Glutte/glutt-o-matique/doc/20151118-machine-etats.png

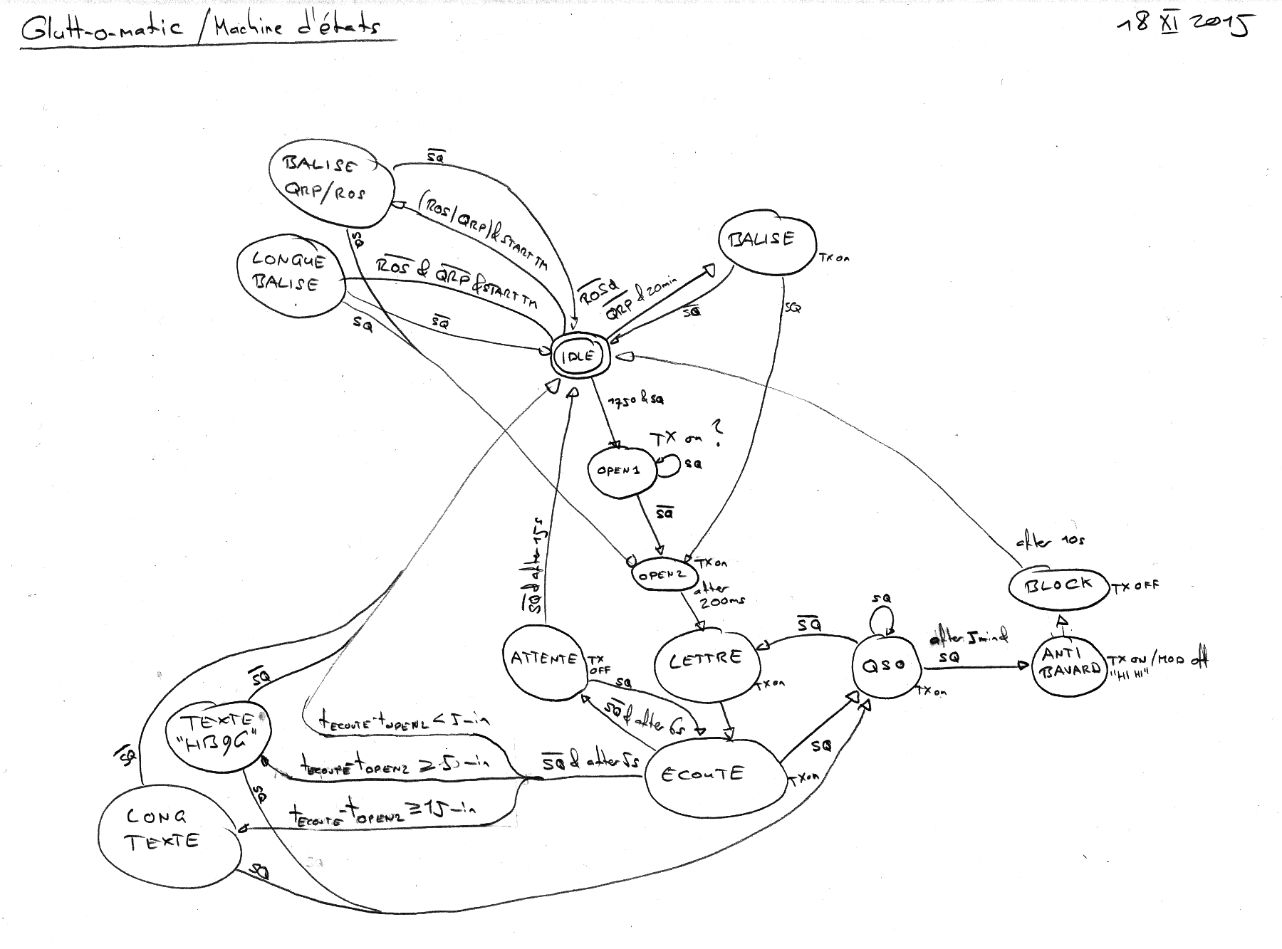
doc/20151118-machine-etats.png
