Glutte/glutt-o-matique/src/common/GPIO/leds.h

#pragma once

#define LED_GREEN 1
#define LED_ORANGE 2
#define LED_RED 3
#define LED_BLUE 4

void leds_turn_off(int);
void leds_turn_on(int);
