Glutte/glutt-o-matique/src/simulator/src/Gui/gui.c

/*
 * The MIT License (MIT)
 *
 * Copyright (c) 2016 Matthias P. Braendli, Maximilien Cuony
 *
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
 * THE SOFTWARE IS PROVIDED "AS IS", WITHOUT WARRANTY OF ANY KIND, EXPRESS OR
 * IMPLIED, INCLUDING BUT NOT LIMITED TO THE WARRANTIES OF MERCHANTABILITY,
 * FITNESS FOR A PARTICULAR PURPOSE AND NONINFRINGEMENT. IN NO EVENT SHALL THE
 * AUTHORS OR COPYRIGHT HOLDERS BE LIABLE FOR ANY CLAIM, DAMAGES OR OTHER
 * LIABILITY, WHETHER IN AN ACTION OF CONTRACT, TORT OR OTHERWISE, ARISING FROM,
 * OUT OF OR IN CONNECTION WITH THE SOFTWARE OR THE USE OR OTHER DEALINGS IN THE
 * SOFTWARE.
*/

#include "FreeRTOS.h"
#include "FreeRTOSConfig.h"
#include "task.h"

#include <stdio.h>
#include <stdlib.h>
#include <stdint.h>
#include <stdarg.h>
#include <string.h>
#include <math.h>
#include <assert.h>
#include <math.h>
#include <time.h>
#include <limits.h>

#include "gui.h"
#include "Core/common.h"

#define NK_INCLUDE_FIXED_TYPES
#define NK_INCLUDE_STANDARD_IO
#define NK_INCLUDE_DEFAULT_ALLOCATOR
#define NK_INCLUDE_VERTEX_BUFFER_OUTPUT
#define NK_INCLUDE_FONT_BAKING
#define NK_INCLUDE_DEFAULT_FONT
#define NK_IMPLEMENTATION
#define NK_XLIB_GL3_IMPLEMENTATION
#define NK_XLIB_LOAD_OPENGL_EXTENSIONS

#pragma GCC diagnostic push 
#pragma GCC diagnostic ignored "-Wunused-but-set-variable"
#pragma GCC diagnostic ignored "-Wunused-value"
#pragma GCC diagnostic ignored "-Wunused-function"
#include "nuklear.h"
#pragma GCC diagnostic pop

#include "nuklear_xlib_gl3.h"

#define WINDOW_WIDTH 1300
#define WINDOW_HEIGHT 800

#define MAX_VERTEX_BUFFER 512 * 1024
#define MAX_ELEMENT_BUFFER 128 * 1024

#define UNUSED(a) (void)a
#define MIN(a,b) ((a) < (b) ? (a) : (b))
#define MAX(a,b) ((a) < (b) ? (b) : (a))
#define LEN(a) (sizeof(a)/sizeof(a)[0])


/**
 * USART
 **/
char uart_recv_txt[4096];
static char uart_send_txt[512];
static int uart_send_txt_len;
void gui_usart_send(char*);

/**
 * Leds
 **/
char led_blue = 0;
char led_green = 0;
char led_orange = 0;
char led_red = 0;
char led_gps = 0;
char led_fax = 0;
char led_det_1750 = 0;
char led_sq2 = 0;

/**
 * GPS
 */
int gui_gps_send_frame = 0;
int gui_gps_frames_valid = 1;
char gui_gps_lat[64] = "4719.59788";
int gui_gps_lat_len = 10;
static const char *gps_NS[] = {"North", "South"};
int gui_gps_lat_hem = 0;
char gui_gps_lon[64] = "00830.92084";
int gui_gps_lon_len = 10;
static const char *gps_EW[] = {"East", "West"};
int gui_gps_lon_hem = 0;
int gui_gps_send_current_time = 1;
int gui_gps_custom_hour_on = 0;
int gui_gps_custom_min_on = 0;
int gui_gps_custom_sec_on = 0;
int gui_gps_custom_day_on = 0;
int gui_gps_custom_month_on = 0;
int gui_gps_custom_year_on = 0;
char gui_gps_custom_hour[4] = "12";
int gui_gps_custom_hour_len = 2;
char gui_gps_custom_min[4] = "30";
int gui_gps_custom_min_len = 2;
char gui_gps_custom_sec[4] = "45";
int gui_gps_custom_sec_len = 2;
char gui_gps_custom_day[4] = "01";
int gui_gps_custom_day_len = 2;
char gui_gps_custom_month[4] = "06";
int gui_gps_custom_month_len = 2;
char gui_gps_custom_year[4] = "16";
int gui_gps_custom_year_len = 2;


/**
 * Audio
 **/
char gui_cw_text[4096];


/**
 * Temperature
 **/
int gui_temperature_valid = 1;
float gui_temperature = 25.0;


/**
 * Outputs
 */
char gui_out_tx = 0;
char gui_out_mod_off = 0;
char gui_out_qrp = 0;


/**
 * Inputs
 */
int gui_in_button = 0;
int gui_in_qrp_n = 1;
int gui_in_1750_n = 1;
int gui_in_sq_n = 1;
int gui_in_u = 0;
int gui_in_d = 0;
int gui_in_replie = 0;
int gui_in_tone_1750 = 0;
static const char *replie_status[] = {"In vent", "Replié"};
int gui_in_fax_n = 1;

int in_button = 0;
int in_qrp_n = 1;
int in_1750_n = 1;
int in_sq_n = 1;
int in_u = 0;
int in_d = 0;
int in_fax_n = 1;


/**
 * FSM
 **/
const char * gui_last_fsm_states[] = {"", "", "", "", "", "", "", "", "", ""};
int gui_last_fsm_states_timestamps[] = {0, 0, 0, 0, 0, 0, 0, 0, 0, 0};


/**
 * Voltage and battery cap
 **/
float gui_measured_voltage = 14.0f;
int gui_measured_capacity = 1630; // Ah
int gui_measured_capacity_last = 1630; // Ah

static const char *breaker_status[] = {"Closed", "Open"};
static const char *breaker_message[] = {"On", "Off"};
int gui_breaker_status = 0;
int gui_breaker_status_last = 0;


/**
 * SWR
 **/
int gui_swr_forward;
int gui_swr_reflected;


int auto_scroll_uart = 1;
int auto_scroll_cw = 1;


struct XWindow {
    Display *dpy;
    Window win;
    XVisualInfo *vis;
    Colormap cmap;
    XSetWindowAttributes swa;
    XWindowAttributes attr;
    GLXFBConfig fbc;
    int width, height;
};

static int gl_err = FALSE;
static int gl_error_handler(Display __attribute__ ((unused))*dpy, XErrorEvent __attribute__ ((unused))*ev) {
    gl_err = TRUE;
    return 0;
}

static void die(const char *fmt, ...) {
    va_list ap;
    va_start(ap, fmt);
    vfprintf(stderr, fmt, ap);
    va_end(ap);
    fputs("\n", stderr);
    exit(EXIT_FAILURE);
}

static int has_extension(const char *string, const char *ext) {

    const char *start, *where, *term;
    where = strchr(ext, ' ');

    if (where || *ext == '\0')
        return FALSE;

    for (start = string;;) {
        where = strstr((const char*)start, ext);
        if (!where) break;

        term = where + strlen(ext);
        if (where == start || *(where - 1) == ' ') {
            if (*term == ' ' || *term == '\0') {
                return TRUE;
            }
        }
        start = term;
    }
    return FALSE;
}


void main_gui() {
    /* Platform */
    int running = 1;
    struct XWindow win;
    GLXContext glContext;
    struct nk_context *ctx;
    struct nk_color background;

    memset(&win, 0, sizeof(win));
    win.dpy = XOpenDisplay(NULL);

    if (!win.dpy) {
        die("Failed to open X display\n");
    }

    {
        /* check glx version */
        int glx_major, glx_minor;
        if (!glXQueryVersion(win.dpy, &glx_major, &glx_minor))
            die("[X11]: Error: Failed to query OpenGL version\n");
        if ((glx_major == 1 && glx_minor < 3) || (glx_major < 1))
            die("[X11]: Error: Invalid GLX version!\n");
    }

    {
        /* find and pick matching framebuffer visual */
        int fb_count;
        static GLint attr[] = {
            GLX_X_RENDERABLE,   True,
            GLX_DRAWABLE_TYPE,  GLX_WINDOW_BIT,
            GLX_RENDER_TYPE,    GLX_RGBA_BIT,
            GLX_X_VISUAL_TYPE,  GLX_TRUE_COLOR,
            GLX_RED_SIZE,       8,
            GLX_GREEN_SIZE,     8,
            GLX_BLUE_SIZE,      8,
            GLX_ALPHA_SIZE,     8,
            GLX_DEPTH_SIZE,     24,
            GLX_STENCIL_SIZE,   8,
            GLX_DOUBLEBUFFER,   True,
            None
        };
        GLXFBConfig *fbc;
        fbc = glXChooseFBConfig(win.dpy, DefaultScreen(win.dpy), attr, &fb_count);

        if (!fbc) {
            die("[X11]: Error: failed to retrieve framebuffer configuration\n");
        }

        {
            /* pick framebuffer with most samples per pixel */
            int i;
            int fb_best = -1;
            int best_num_samples = -1;

            for (i = 0; i < fb_count; ++i) {
                XVisualInfo *vi = glXGetVisualFromFBConfig(win.dpy, fbc[i]);
                if (vi) {
                    int sample_buffer, samples;
                    glXGetFBConfigAttrib(win.dpy, fbc[i], GLX_SAMPLE_BUFFERS, &sample_buffer);
                    glXGetFBConfigAttrib(win.dpy, fbc[i], GLX_SAMPLES, &samples);
                    if ((fb_best < 0) || (sample_buffer && samples > best_num_samples)) {
                        fb_best = i; best_num_samples = samples;
                    }
                }
            }
            win.fbc = fbc[fb_best];
            XFree(fbc);
            win.vis = glXGetVisualFromFBConfig(win.dpy, win.fbc);
        }
    }
    {
        /* create window */
        win.cmap = XCreateColormap(win.dpy, RootWindow(win.dpy, win.vis->screen), win.vis->visual, AllocNone);
        win.swa.colormap =  win.cmap;
        win.swa.background_pixmap = None;
        win.swa.border_pixel = 0;
        win.swa.event_mask =
            ExposureMask | KeyPressMask | KeyReleaseMask |
            ButtonPress | ButtonReleaseMask| ButtonMotionMask |
            Button1MotionMask | Button3MotionMask | Button4MotionMask | Button5MotionMask|
            PointerMotionMask| StructureNotifyMask;

        win.win = XCreateWindow(win.dpy, RootWindow(win.dpy, win.vis->screen), 0, 0,
                WINDOW_WIDTH, WINDOW_HEIGHT, 0, win.vis->depth, InputOutput,
                win.vis->visual, CWBorderPixel|CWColormap|CWEventMask, &win.swa);

        if (!win.win) die("[X11]: Failed to create window\n");
        XFree(win.vis);
        XStoreName(win.dpy, win.win, "glutt-o-matique simulator 3000");
        XMapWindow(win.dpy, win.win);
    }
    {
        /* create opengl context */
        typedef GLXContext(*glxCreateContext)(Display*, GLXFBConfig, GLXContext, Bool, const int*);
        int(*old_handler)(Display*, XErrorEvent*) = XSetErrorHandler(gl_error_handler);
        const char *extensions_str = glXQueryExtensionsString(win.dpy, DefaultScreen(win.dpy));
        glxCreateContext create_context = (glxCreateContext)
            glXGetProcAddressARB((const GLubyte*)"glXCreateContextAttribsARB");

        gl_err = FALSE;
        if (!has_extension(extensions_str, "GLX_ARB_create_context") || !create_context) {
            fprintf(stdout, "[X11]: glXCreateContextAttribARB() not found...\n");
            fprintf(stdout, "[X11]: ... using old-style GLX context\n");
            glContext = glXCreateNewContext(win.dpy, win.fbc, GLX_RGBA_TYPE, 0, True);
        } else {
            GLint attr[] = {
                GLX_CONTEXT_MAJOR_VERSION_ARB, 3,
                GLX_CONTEXT_MINOR_VERSION_ARB, 0,
                None
            };
            glContext = create_context(win.dpy, win.fbc, 0, True, attr);
            XSync(win.dpy, False);
            if (gl_err || !glContext) {
                /* Could not create GL 3.0 context. Fallback to old 2.x context.
                 * If a version below 3.0 is requested, implementations will
                 * return the newest context version compatible with OpenGL
                 * version less than version 3.0.*/
                attr[1] = 1; attr[3] = 0;
                gl_err = FALSE;
                fprintf(stdout, "[X11] Failed to create OpenGL 3.0 context\n");
                fprintf(stdout, "[X11] ... using old-style GLX context!\n");
                glContext = create_context(win.dpy, win.fbc, 0, True, attr);
            }
        }
        XSync(win.dpy, False);
        XSetErrorHandler(old_handler);
        if (gl_err || !glContext)
            die("[X11]: Failed to create an OpenGL context\n");
        glXMakeCurrent(win.dpy, win.win, glContext);
    }

    ctx = nk_x11_init(win.dpy, win.win);
    /* Load Fonts: if none of these are loaded a default font will be used  */
    {struct nk_font_atlas *atlas;
        nk_x11_font_stash_begin(&atlas);
        nk_x11_font_stash_end();
    }


    background = nk_rgb(28,48,62);

    while (running)
    {
        taskYIELD();

        vTaskSuspendAll();

        /* Input */
        XEvent evt;
        nk_input_begin(ctx);
        while (XCheckWindowEvent(win.dpy, win.win, win.swa.event_mask, &evt)){
            if (XFilterEvent(&evt, win.win)) continue;
            nk_x11_handle_event(&evt);
        }
        nk_input_end(ctx);

        /* GUI */
        {

            struct nk_panel layout;
            int nb_lines = 0;

            if (nk_begin(ctx, &layout, "UART", nk_rect(50, 50, 450, 330), NK_WINDOW_BORDER|NK_WINDOW_MOVABLE|NK_WINDOW_SCALABLE|NK_WINDOW_MINIMIZABLE|NK_WINDOW_TITLE)) {


                nk_menubar_begin(ctx);
                nk_layout_row_begin(ctx, NK_STATIC, 25, 2);
                nk_layout_row_push(ctx, 280);

                int active = nk_edit_string(ctx, NK_EDIT_FIELD|NK_EDIT_SIG_ENTER, uart_send_txt, &uart_send_txt_len, 512,  nk_filter_default);

                nk_layout_row_push(ctx, 70);
                if (nk_button_label(ctx, "Send", NK_BUTTON_DEFAULT) || (active & NK_EDIT_COMMITED)) {

                    uart_send_txt[uart_send_txt_len] = '\0';

                    gui_usart_send(uart_send_txt);

                    uart_send_txt[0] = '\0';
                    uart_send_txt_len = 0;
                }


                nk_layout_row_dynamic(ctx, 25, 2);
                nk_label(ctx, "UART Output:", NK_TEXT_LEFT);
                nk_checkbox_label(ctx, "(Auto scroll)", &auto_scroll_uart);

                nk_menubar_end(ctx);

                nk_layout_row_dynamic(ctx, 16, 1);

                char * current_pointer = uart_recv_txt;
                int l = 0;

                while (*current_pointer != 0) {

                    if (*current_pointer == '\n') {
                        if (l > 1) {
                            nk_text(ctx, current_pointer - l, l, NK_TEXT_LEFT);
                            nb_lines++;
                        }
                        current_pointer++;
                        l = 0;
                    }
                    current_pointer++;
                    l++;
                }

                if (l > 1) {
                    nk_text(ctx, current_pointer - l, l, NK_TEXT_LEFT);
                    nb_lines++;
                }
            }
            if (auto_scroll_uart) {
                layout.offset->y = nb_lines * 32 + 200;
            }
            nk_end(ctx);


            if (nk_begin(ctx, &layout, "LEDs", nk_rect(50, 390, 150, 155), NK_WINDOW_BORDER|NK_WINDOW_MOVABLE|NK_WINDOW_SCALABLE|NK_WINDOW_MINIMIZABLE|NK_WINDOW_TITLE)) {

                nk_layout_row_static(ctx, 20, 20, 5);
                struct nk_color color;

                color.r = 255; color.g = 165; color.b = 0;
                if (led_orange == 1) {
                    color.a = 255;
                } else {
                    color.a = 30;
                }
                nk_button_color(ctx, color, NK_BUTTON_DEFAULT);

                color.r = 0; color.g = 255; color.b = 0;
                if (led_green == 1) {
                    color.a = 255;
                } else {
                    color.a = 30;
                }
                nk_button_color(ctx, color, NK_BUTTON_DEFAULT);

                color.r = 255; color.g = 0; color.b = 0;
                if (led_red == 1) {
                    color.a = 255;
                } else {
                    color.a = 30;
                }
                nk_button_color(ctx, color, NK_BUTTON_DEFAULT);

                color.r = 0; color.g = 0; color.b = 255;
                if (led_blue == 1) {
                    color.a = 255;
                } else {
                    color.a = 30;
                }
                nk_button_color(ctx, color, NK_BUTTON_DEFAULT);

#define SW_LED(var, name) \
                nk_layout_row_static(ctx, 20, 20, 5); \
                color.r = 0; color.g = 255; color.b = 255; \
                if (var == 1) { color.a = 255; } else { color.a = 30; } \
                nk_button_color(ctx, color, NK_BUTTON_DEFAULT); \
                nk_label(ctx, name, NK_TEXT_LEFT);

                SW_LED(led_gps, "GPS")
                SW_LED(led_fax, "FAX")
                SW_LED(led_det_1750, "TONE")
                SW_LED(led_sq2, "SQ2")

            }
            nk_end(ctx);

            if (nk_begin(ctx, &layout, "CW", nk_rect(320, 390, 180, 155), NK_WINDOW_BORDER|NK_WINDOW_MOVABLE|NK_WINDOW_SCALABLE|NK_WINDOW_MINIMIZABLE|NK_WINDOW_TITLE)) {

                nk_menubar_begin(ctx);
                nk_layout_row_dynamic(ctx, 25, 2);

                nk_label(ctx, "CW Buffer:", NK_TEXT_LEFT);
                nk_checkbox_label(ctx, "(Auto scroll)", &auto_scroll_cw);

                nk_menubar_end(ctx);

                nk_layout_row_dynamic(ctx, 16, 1);

                char * current_pointer = gui_cw_text;
                int l = 0;
                nb_lines = 0;

                while (*current_pointer != 0) {

                    if (*current_pointer == '\n') {
                        if (l > 1) {
                            nk_text(ctx, current_pointer - l, l, NK_TEXT_LEFT);
                            nb_lines++;
                        }
                        current_pointer++;
                        l = 0;
                    }
                    current_pointer++;
                    l++;
                }

                if (l > 1) {
                    nk_text(ctx, current_pointer - l, l, NK_TEXT_LEFT);
                    nb_lines++;
                }
            }
            if (auto_scroll_uart) {
                layout.offset->y = nb_lines * 32 + 200;
            }
            nk_end(ctx);

            if (nk_begin(ctx, &layout, "GPS", nk_rect(510, 50, 200, 500), NK_WINDOW_BORDER|NK_WINDOW_MOVABLE|NK_WINDOW_MINIMIZABLE|NK_WINDOW_TITLE)) {

                nk_layout_row_dynamic(ctx, 30, 1);
                nk_checkbox_label(ctx, "Send frames", &gui_gps_send_frame);
                nk_checkbox_label(ctx, "Valid frames", &gui_gps_frames_valid);

                nk_layout_row_dynamic(ctx, 30, 2);

                nk_label(ctx, "Latitude:", NK_TEXT_LEFT);
                nk_edit_string(ctx, NK_EDIT_SIMPLE, gui_gps_lat, &gui_gps_lat_len, 64, nk_filter_float);
                nk_label(ctx, "", NK_TEXT_LEFT);
                gui_gps_lat_hem = nk_combo(ctx, gps_NS, LEN(gps_NS), gui_gps_lat_hem, 30);

                nk_label(ctx, "Longitude:", NK_TEXT_LEFT);
                nk_edit_string(ctx, NK_EDIT_SIMPLE, gui_gps_lon, &gui_gps_lon_len, 64, nk_filter_float);
                nk_label(ctx, "", NK_TEXT_LEFT);
                gui_gps_lon_hem = nk_combo(ctx, gps_EW, LEN(gps_EW), gui_gps_lon_hem, 30);

                nk_layout_row_dynamic(ctx, 30, 1);
                nk_checkbox_label(ctx, "Send current time", &gui_gps_send_current_time);

                if (!gui_gps_send_current_time) {

                    nk_label(ctx, "Custom values:", NK_TEXT_LEFT);

                    nk_layout_row_dynamic(ctx, 30, 3);

                    nk_label(ctx, "Hour", NK_TEXT_LEFT);
                    nk_checkbox_label(ctx, "", &gui_gps_custom_hour_on);
                    if (gui_gps_custom_hour_on) {
                        nk_edit_string(ctx, NK_EDIT_SIMPLE, gui_gps_custom_hour, &gui_gps_custom_hour_len, 3, nk_filter_decimal);
                    } else {
                        nk_label(ctx, "", NK_TEXT_LEFT);
                    }
                    nk_label(ctx, "Minutes", NK_TEXT_LEFT);
                    nk_checkbox_label(ctx, "", &gui_gps_custom_min_on);
                    if (gui_gps_custom_min_on) {
                        nk_edit_string(ctx, NK_EDIT_SIMPLE, gui_gps_custom_min, &gui_gps_custom_min_len, 3, nk_filter_decimal);
                    } else {
                        nk_label(ctx, "", NK_TEXT_LEFT);
                    }
                    nk_label(ctx, "Secondes", NK_TEXT_LEFT);
                    nk_checkbox_label(ctx, "", &gui_gps_custom_sec_on);
                    if (gui_gps_custom_sec_on) {
                        nk_edit_string(ctx, NK_EDIT_SIMPLE, gui_gps_custom_sec, &gui_gps_custom_sec_len, 3, nk_filter_decimal);
                    } else {
                        nk_label(ctx, "", NK_TEXT_LEFT);
                    }
                    nk_label(ctx, "Day", NK_TEXT_LEFT);
                    nk_checkbox_label(ctx, "", &gui_gps_custom_day_on);
                    if (gui_gps_custom_day_on) {
                        nk_edit_string(ctx, NK_EDIT_SIMPLE, gui_gps_custom_day, &gui_gps_custom_day_len, 3, nk_filter_decimal);
                    } else {
                        nk_label(ctx, "", NK_TEXT_LEFT);
                    }
                    nk_label(ctx, "Month", NK_TEXT_LEFT);
                    nk_checkbox_label(ctx, "", &gui_gps_custom_month_on);
                    if (gui_gps_custom_month_on) {
                        nk_edit_string(ctx, NK_EDIT_SIMPLE, gui_gps_custom_month, &gui_gps_custom_month_len, 3, nk_filter_decimal);
                    } else {
                        nk_label(ctx, "", NK_TEXT_LEFT);
                    }
                    nk_label(ctx, "Year", NK_TEXT_LEFT);
                    nk_checkbox_label(ctx, "", &gui_gps_custom_year_on);
                    if (gui_gps_custom_year_on) {
                        nk_edit_string(ctx, NK_EDIT_SIMPLE, gui_gps_custom_year, &gui_gps_custom_year_len, 3, nk_filter_decimal);
                    } else {
                        nk_label(ctx, "", NK_TEXT_LEFT);
                    }


                }

            }
            nk_end(ctx);


            if (nk_begin(ctx, &layout, "Output", nk_rect(720, 510, 200, 170), NK_WINDOW_BORDER|NK_WINDOW_MOVABLE|NK_WINDOW_MINIMIZABLE|NK_WINDOW_TITLE)) {

                nk_layout_row_dynamic(ctx, 25, 2);

                struct nk_color color;

                nk_label(ctx, "TX", NK_TEXT_LEFT);

                color.r = 0; color.g = 255; color.b = 0;

                if (gui_out_tx == 1) {
                    color.a = 255;
                } else {
                    color.a = 30;
                }
                nk_button_color(ctx, color, NK_BUTTON_DEFAULT);

                nk_label(ctx, "Mod OFF", NK_TEXT_LEFT);

                color.r = 255; color.g = 255; color.b = 0;

                if (gui_out_mod_off == 1) {
                    color.a = 255;
                } else {
                    color.a = 30;
                }
                nk_button_color(ctx, color, NK_BUTTON_DEFAULT);

                nk_label(ctx, "QRP", NK_TEXT_LEFT);

                color.r = 255; color.g = 0; color.b = 0;

                if (gui_out_qrp == 1) {
                    color.a = 255;
                } else {
                    color.a = 30;
                }
                nk_button_color(ctx, color, NK_BUTTON_DEFAULT);

            }
            nk_end(ctx);

            if (nk_begin(ctx, &layout, "Input", nk_rect(720, 50, 200, 460), NK_WINDOW_BORDER|NK_WINDOW_MOVABLE|NK_WINDOW_MINIMIZABLE|NK_WINDOW_TITLE)) {

                nk_layout_row_dynamic(ctx, 25, 3);

                struct nk_color color_on = nk_rgb(0, 255, 0);
                struct nk_color color_off = nk_rgb(255, 0, 0);

                struct nk_color c;

                if (gui_in_button) {
                    c = color_on;
                } else {
                    c = color_off;
                }

                nk_label_colored(ctx, "Button", NK_TEXT_LEFT, c);
                nk_checkbox_label(ctx, "", &in_button);

                if (nk_button_label(ctx, "", NK_BUTTON_REPEATER)) {
                    gui_in_button = !in_button;
                } else {
                    gui_in_button = in_button;
                }

                if (gui_in_qrp_n) {
                    c = color_on;
                } else {
                    c = color_off;
                }

                nk_label_colored(ctx, "QRP_n", NK_TEXT_LEFT, c);
                nk_checkbox_label(ctx, "", &in_qrp_n);

                if (nk_button_label(ctx, "", NK_BUTTON_REPEATER)) {
                    gui_in_qrp_n = !in_qrp_n;
                } else {
                    gui_in_qrp_n = in_qrp_n;
                }

                if (gui_in_1750_n) {
                    c = color_on;
                } else {
                    c = color_off;
                }

                nk_label_colored(ctx, "1750 btn", NK_TEXT_LEFT, c);
                nk_checkbox_label(ctx, "", &in_1750_n);

                if (nk_button_label(ctx, "", NK_BUTTON_REPEATER)) {
                    gui_in_1750_n = !in_1750_n;
                } else {
                    gui_in_1750_n = in_1750_n;
                }

                if (gui_in_sq_n) {
                    c = color_on;
                } else {
                    c = color_off;
                }

                nk_label_colored(ctx, "SQ_n", NK_TEXT_LEFT, c);
                nk_checkbox_label(ctx, "", &in_sq_n);

                if (nk_button_label(ctx, "", NK_BUTTON_REPEATER)) {
                    gui_in_sq_n = !in_sq_n;
                } else {
                    gui_in_sq_n = in_sq_n;
                }

                if (gui_in_u) {
                    c = color_on;
                } else {
                    c = color_off;
                }

                nk_label_colored(ctx, "U", NK_TEXT_LEFT, c);
                nk_checkbox_label(ctx, "", &in_u);

                if (nk_button_label(ctx, "", NK_BUTTON_REPEATER)) {
                    gui_in_u = !in_u;
                } else {
                    gui_in_u = in_u;
                }

                if (gui_in_d) {
                    c = color_on;
                } else {
                    c = color_off;
                }

                nk_label_colored(ctx, "D", NK_TEXT_LEFT, c);
                nk_checkbox_label(ctx, "", &in_d);

                if (nk_button_label(ctx, "", NK_BUTTON_REPEATER)) {
                    gui_in_d = !in_d;
                } else {
                    gui_in_d = in_d;
                }

                if (gui_in_fax_n) {
                    c = color_on;
                } else {
                    c = color_off;
                }

                nk_label_colored(ctx, "FAX_n", NK_TEXT_LEFT, c);
                nk_checkbox_label(ctx, "", &in_fax_n);

                if (nk_button_label(ctx, "", NK_BUTTON_REPEATER)) {
                    gui_in_fax_n = !in_fax_n;
                } else {
                    gui_in_fax_n = in_fax_n;
                }

                if (gui_in_replie) {
                    c = color_on;
                } else {
                    c = color_off;
                }

                nk_layout_row_dynamic(ctx, 18, 2);
                nk_label_colored(ctx, "REPLIE", NK_TEXT_LEFT, c);
                gui_in_replie = nk_combo(ctx, replie_status, LEN(replie_status), gui_in_replie, 30);

                nk_label_colored(ctx, "Voltage", NK_TEXT_LEFT, c);
                nk_property_float(ctx, "V", 0.0f, &gui_measured_voltage, 24.0f, 0.5f, 0.5f);

                nk_layout_row_dynamic(ctx, 25, 2);
                nk_label_colored(ctx, "Eolienne breaker", NK_TEXT_LEFT, c);
                gui_breaker_status = nk_combo(ctx, breaker_status, LEN(breaker_status), gui_breaker_status, 30);

                if (gui_breaker_status != gui_breaker_status_last) {
                    uart_send_txt_len = snprintf(uart_send_txt, sizeof(uart_send_txt), "DISJEOL,%ld,%s", timestamp_now()/1000, breaker_message[gui_breaker_status]);

                    uart_send_txt[uart_send_txt_len] = '\0';
                    gui_usart_send(uart_send_txt);

                    gui_breaker_status_last = gui_breaker_status;
                }

                nk_layout_row_dynamic(ctx, 25, 2);
                nk_label_colored(ctx, "Capacity", NK_TEXT_LEFT, c);
                nk_property_int(ctx, "Ah", 0, &gui_measured_capacity, 1650, 10, 0.1f);

                if (gui_measured_capacity != gui_measured_capacity_last) {
                    uart_send_txt_len = snprintf(uart_send_txt, sizeof(uart_send_txt), "CAPA,%ld,%d", timestamp_now()/1000, gui_measured_capacity * 1000);

                    uart_send_txt[uart_send_txt_len] = '\0';
                    gui_usart_send(uart_send_txt);

                    gui_measured_capacity_last = gui_measured_capacity;
                }

                if (gui_in_tone_1750) {
                    c = color_on;
                } else {
                    c = color_off;
                }

                nk_label_colored(ctx, "TONE_1750", NK_TEXT_LEFT, c);


            }
            nk_end(ctx);

            if (nk_begin(ctx, &layout, "Temperature", nk_rect(930, 50, 200, 140), NK_WINDOW_BORDER|NK_WINDOW_MOVABLE|NK_WINDOW_MINIMIZABLE|NK_WINDOW_TITLE)) {

                nk_layout_row_dynamic(ctx, 25, 1);

                nk_checkbox_label(ctx, "Valid temperature", &gui_temperature_valid);

                if (gui_temperature_valid) {

                    nk_layout_row_dynamic(ctx, 25, 2);

                    nk_label(ctx, "Temperature", NK_TEXT_LEFT);
                    nk_property_float(ctx, "°C", -20.0f, &gui_temperature, 50.0f, 0.1f, 0.5f);
                }

            }
            nk_end(ctx);

            if (nk_begin(ctx, &layout, "FSM", nk_rect(930, 200, 300, 350), NK_WINDOW_BORDER|NK_WINDOW_MOVABLE|NK_WINDOW_MINIMIZABLE|NK_WINDOW_SCALABLE|NK_WINDOW_TITLE)) {

                nk_layout_row_dynamic(ctx, 25, 2);

                for (int i = 0; i < 9; i++) {
                    nk_label(ctx, gui_last_fsm_states[i], NK_TEXT_LEFT);

                    char buffer[50];

                    int v = gui_last_fsm_states_timestamps[i];

                    if (v > 0) {

                        int hours = v / 10000;
                        v -= hours * 10000;
                        int minutes = v / 100;
                        v -= minutes * 100;
                        int seconds = v;

                        sprintf(buffer, "%02d:%02d:%02d", hours, minutes, seconds);

                    } else {
                        buffer[0] = '\0';
                    }
                    nk_label(ctx, buffer, NK_TEXT_RIGHT);

                }

            }
            nk_end(ctx);

            if (nk_begin(ctx, &layout, "SWR", nk_rect(50, 555, 350, 155), NK_WINDOW_BORDER|NK_WINDOW_MOVABLE|NK_WINDOW_MINIMIZABLE|NK_WINDOW_TITLE)) {


                    nk_layout_row_dynamic(ctx, 25, 2);

                    nk_label(ctx, "Forward", NK_TEXT_LEFT);
                    nk_property_int(ctx, "?", 0, &gui_swr_forward, 65536, 1, 1);

                    nk_label(ctx, "Reflected", NK_TEXT_LEFT);
                    nk_property_int(ctx, "??", 0, &gui_swr_reflected, 65536, 1, 1);
            }
            nk_end(ctx);

        }

        {
            float bg[4];
            nk_color_fv(bg, background);
            XGetWindowAttributes(win.dpy, win.win, &win.attr);
            glViewport(0, 0, win.width, win.height);
            glClear(GL_COLOR_BUFFER_BIT);
            glClearColor(bg[0], bg[1], bg[2], bg[3]);
            nk_x11_render(NK_ANTI_ALIASING_ON, MAX_VERTEX_BUFFER, MAX_ELEMENT_BUFFER);
            glXSwapBuffers(win.dpy, win.win);
        }

        xTaskResumeAll();
    }

    nk_x11_shutdown();
    glXMakeCurrent(win.dpy, 0, 0);
    glXDestroyContext(win.dpy, glContext);
    XUnmapWindow(win.dpy, win.win);
    XFreeColormap(win.dpy, win.cmap);
    XDestroyWindow(win.dpy, win.win);
    XCloseDisplay(win.dpy);

}
